DimitriiTkachreal/Thermostat_Tkach/Software/mcu/timer.c

/**
 * @file    timer.c
 * @brief   Реалізація апаратного відліку часу та обробника переривання.
 */

#include "timer.h"

/* ========================================================================== */
/* ГЛОБАЛЬНІ ЗМІННІ МОДУЛЯ                                                    */
/* ========================================================================== */

/* * Глобальний лічильник мілісекунд.
 * static   - закриває доступ до змінної з інших файлів (Інкапсуляція).
 * volatile - забороняє компілятору оптимізувати (видаляти) змінну, 
 * оскільки вона змінюється апаратно в перериванні.
 */
static volatile uint32_t sys_tick_ms = 0;


/* ========================================================================== */
/* 1. НАЛАШТУВАННЯ ТАЙМЕРА (ІНІЦІАЛІЗАЦІЯ)                                    */
/* ========================================================================== */

void Timer4_Init(void) 
{
    /* ---------------------------------------------------------------------- */
    /* КРОК 1: Налаштування частоти (Prescaler)                               */
    /* ---------------------------------------------------------------------- */
    /* Базова частота = 16 МГц. Записуємо 0x07 (дільник 128).                 */
    /* 16 000 000 / 128 = 125 000 тактів на секунду.                          */
    TIM4_PSCR = 0x07; 
    
    /* ---------------------------------------------------------------------- */
    /* КРОК 2: Встановлення межі (Auto-Reload)                                */
    /* ---------------------------------------------------------------------- */
    /* Щоб отримати 1 мілісекунду, нам треба відрахувати 125 тактів.          */
    TIM4_ARR = 124;   
    
    /* ---------------------------------------------------------------------- */
    /* КРОК 3: Увімкнення переривань та старту                                */
    /* ---------------------------------------------------------------------- */
    /* Дозволяємо таймеру генерувати сигнал (Update Interrupt Enable)         */
    TIM4_IER |= 0x01;  
    
    /* Запускаємо лічильник таймера (Counter Enable)                          */
    TIM4_CR1 |= 0x01;  
}


/* ========================================================================== */
/* 2. РЕАЛІЗАЦІЯ БІЗНЕС-ЛОГІКИ (ЧИТАННЯ ЧАСУ)                                 */
/* ========================================================================== */

uint32_t Timer_GetMillis(void) 
{
    uint32_t current_ms;
    
    /* АТОМАРНА ОПЕРАЦІЯ: Вимикаємо глобальні переривання.
     * Оскільки STM8 - 8-бітний, він читає 32-бітну змінну за 4 кроки. 
     * Якщо під час читання спрацює таймер, число "розірветься". */
    _asm("sim"); 
    
    /* Спокійно копіюємо час, знаючи, що залізо нас не переб'є */
    current_ms = sys_tick_ms;
    
    /* Вмикаємо переривання назад */
    _asm("rim");
    
    return current_ms;
}


/* ========================================================================== */
/* 3. ФУНКЦІЯ ОБРОБНИКА ПЕРЕРИВАННЯ (ISR)                                     */
/* ========================================================================== */

/* Вказуємо компілятору покласти адресу цієї функції у 25-й вектор (TIM4)     */
#pragma vector = 25
@far @interrupt void TIM4_UPD_OVF_IRQHandler(void) 
{
    /* ОБОВ'ЯЗКОВО: Скидаємо прапорець переривання в залізі, 
     * інакше Ядро зациклиться в цій функції назавжди. */
    TIM4_SR &= (uint8_t)(~0x01);

    /* Корисна дія: додаємо 1 мілісекунду */
    sys_tick_ms++;
}
